chickadee-tech/g-test-bot/f4_control_test/F4Test.ioc

Mcu.UserName=STM32F405VGTx
PA5.Signal=SPI1_SCK
PA6.Signal=SPI1_MISO
PA7.Signal=SPI1_MOSI
PD8.Signal=USART3_TX
PD9.Signal=USART3_RX
PH0-OSC_IN.Signal=RCC_OSC_IN
PH1-OSC_OUT.Signal=RCC_OSC_OUT
